Pronoe/millihom-meter/pcb_Kicad/pcb.jpg

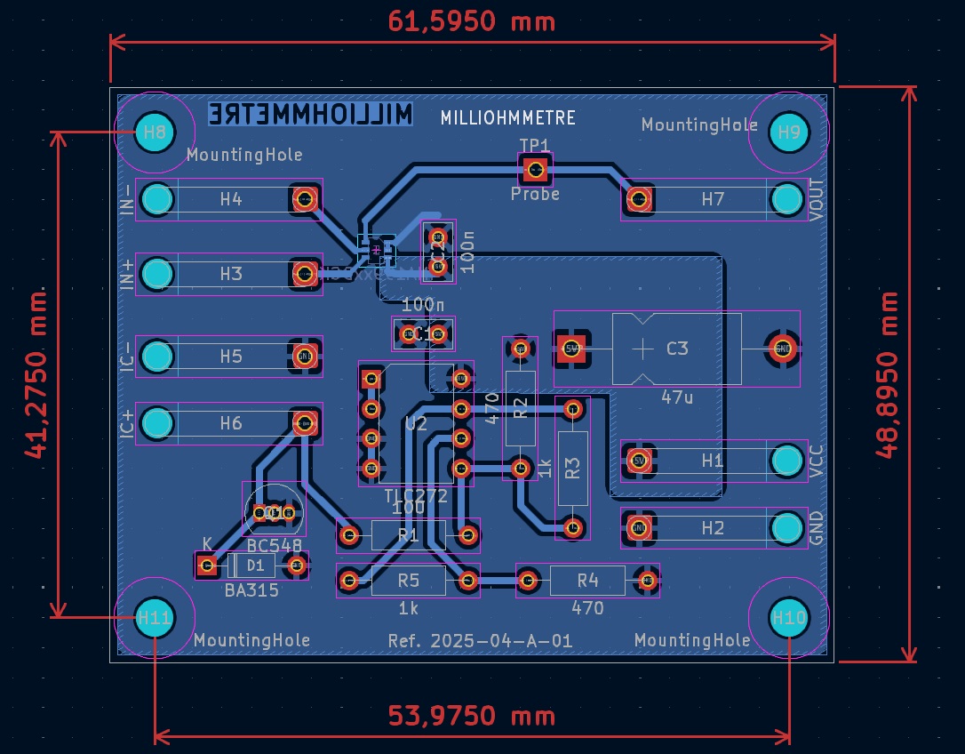
pcb_Kicad/pcb.jpg
