Pronoe/millihom-meter/pictures/20250501_192320 (FILEminimizer).jpg

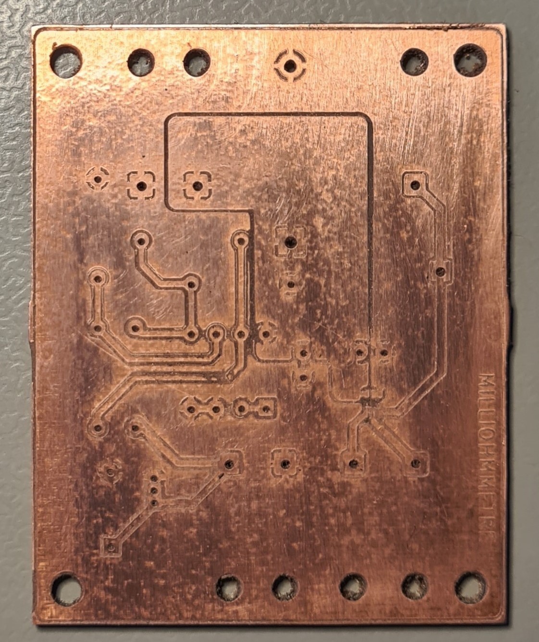
pictures/20250501_192320 (FILEminimizer).jpg
