Pronoe/millihom-meter/pictures/20250503_223159 (FILEminimizer).jpg

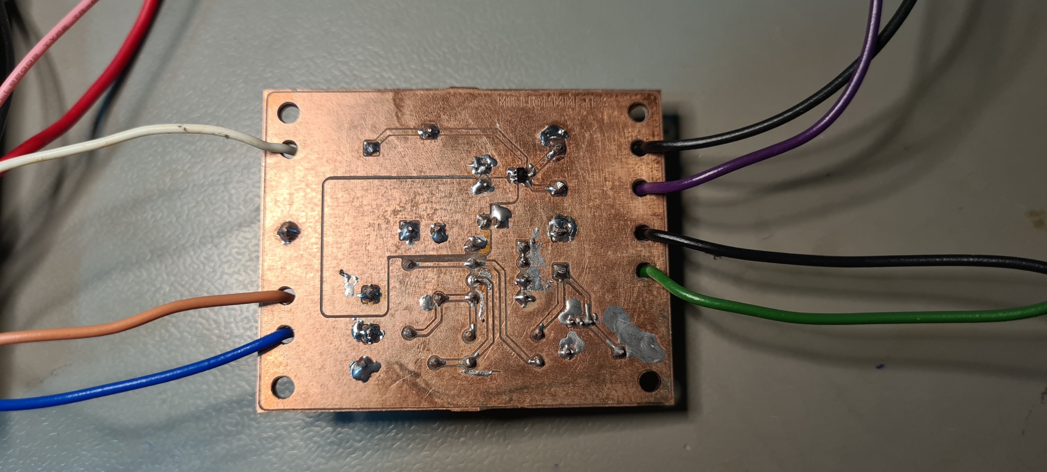
pictures/20250503_223159 (FILEminimizer).jpg
