Pronoe/millihom-meter/pictures/20250512_212327 (FILEminimizer).jpg

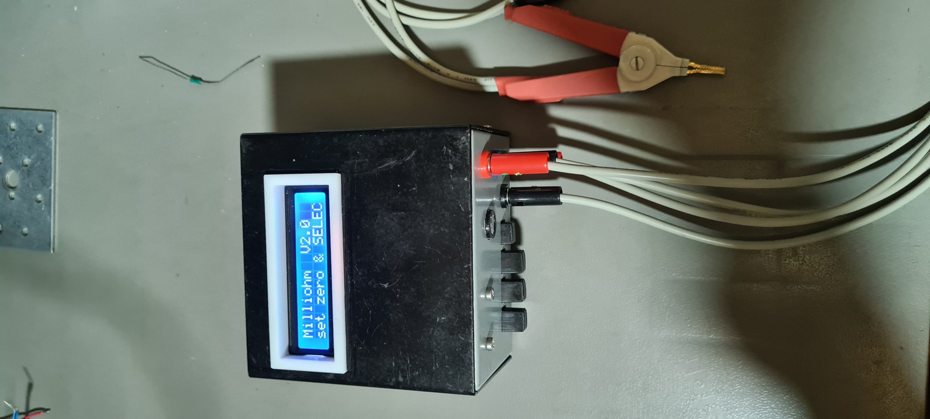
pictures/20250512_212327 (FILEminimizer).jpg
