Pronoe/millihom-meter/pictures/20250512_212805 (FILEminimizer).jpg

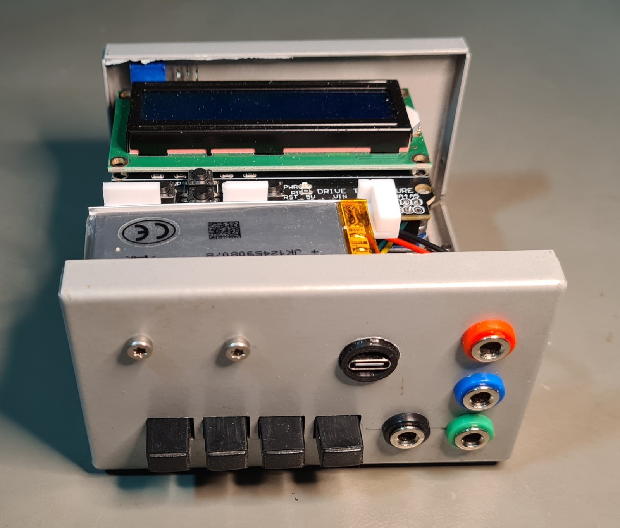
pictures/20250512_212805 (FILEminimizer).jpg
