Pronoe/millihom-meter/pictures/20250512_212813 (FILEminimizer).jpg

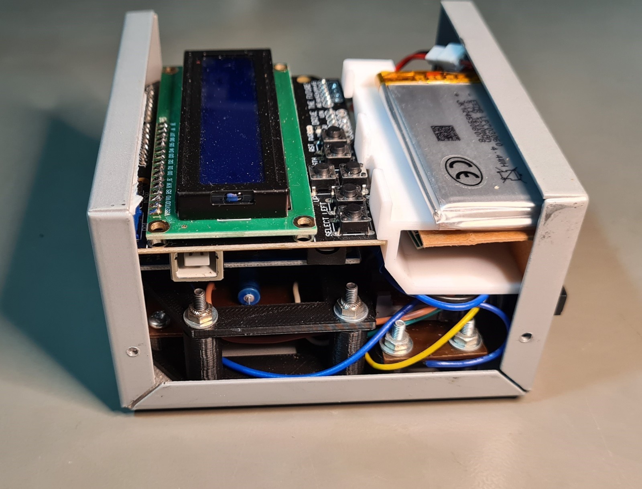
pictures/20250512_212813 (FILEminimizer).jpg
