Pronoe/millihom-meter/pictures/20250512_212826 (FILEminimizer).jpg

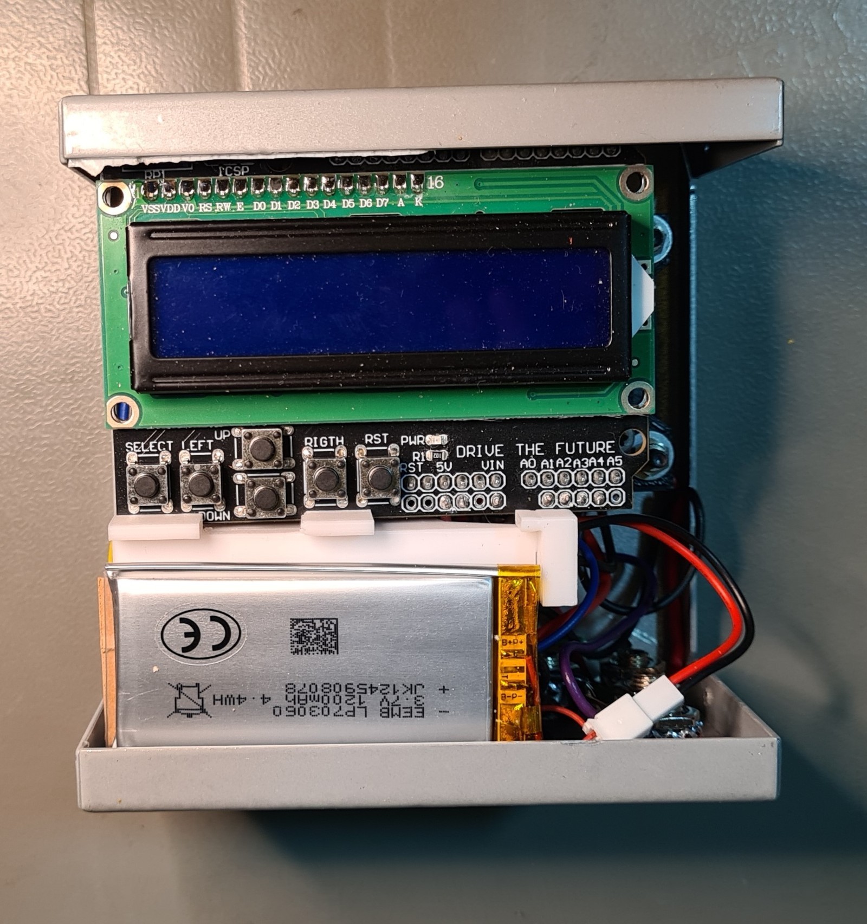
pictures/20250512_212826 (FILEminimizer).jpg
