Pronoe/millihom-meter/pictures/20250522_191747 (FILEminimizer).jpg

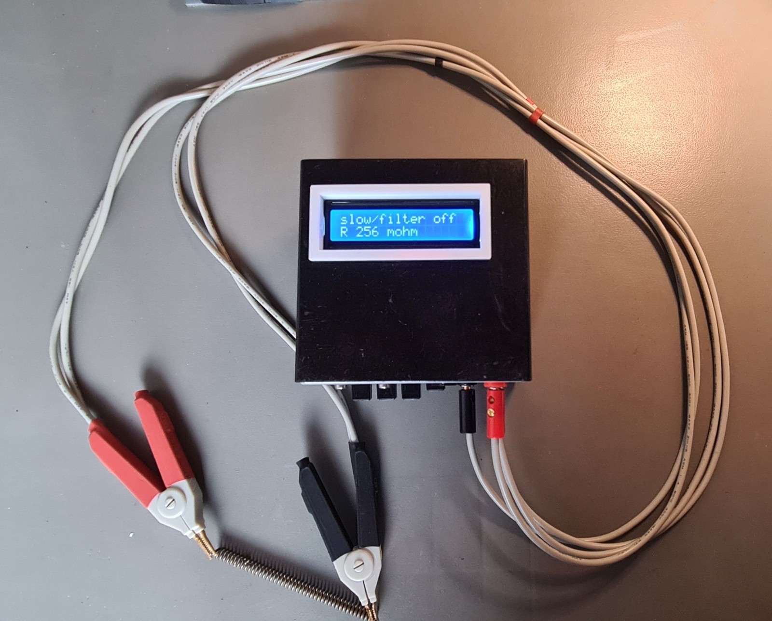
pictures/20250522_191747 (FILEminimizer).jpg
