Pronoe/millihom-meter/SW Arduino/Diagramme_SW_V1.png

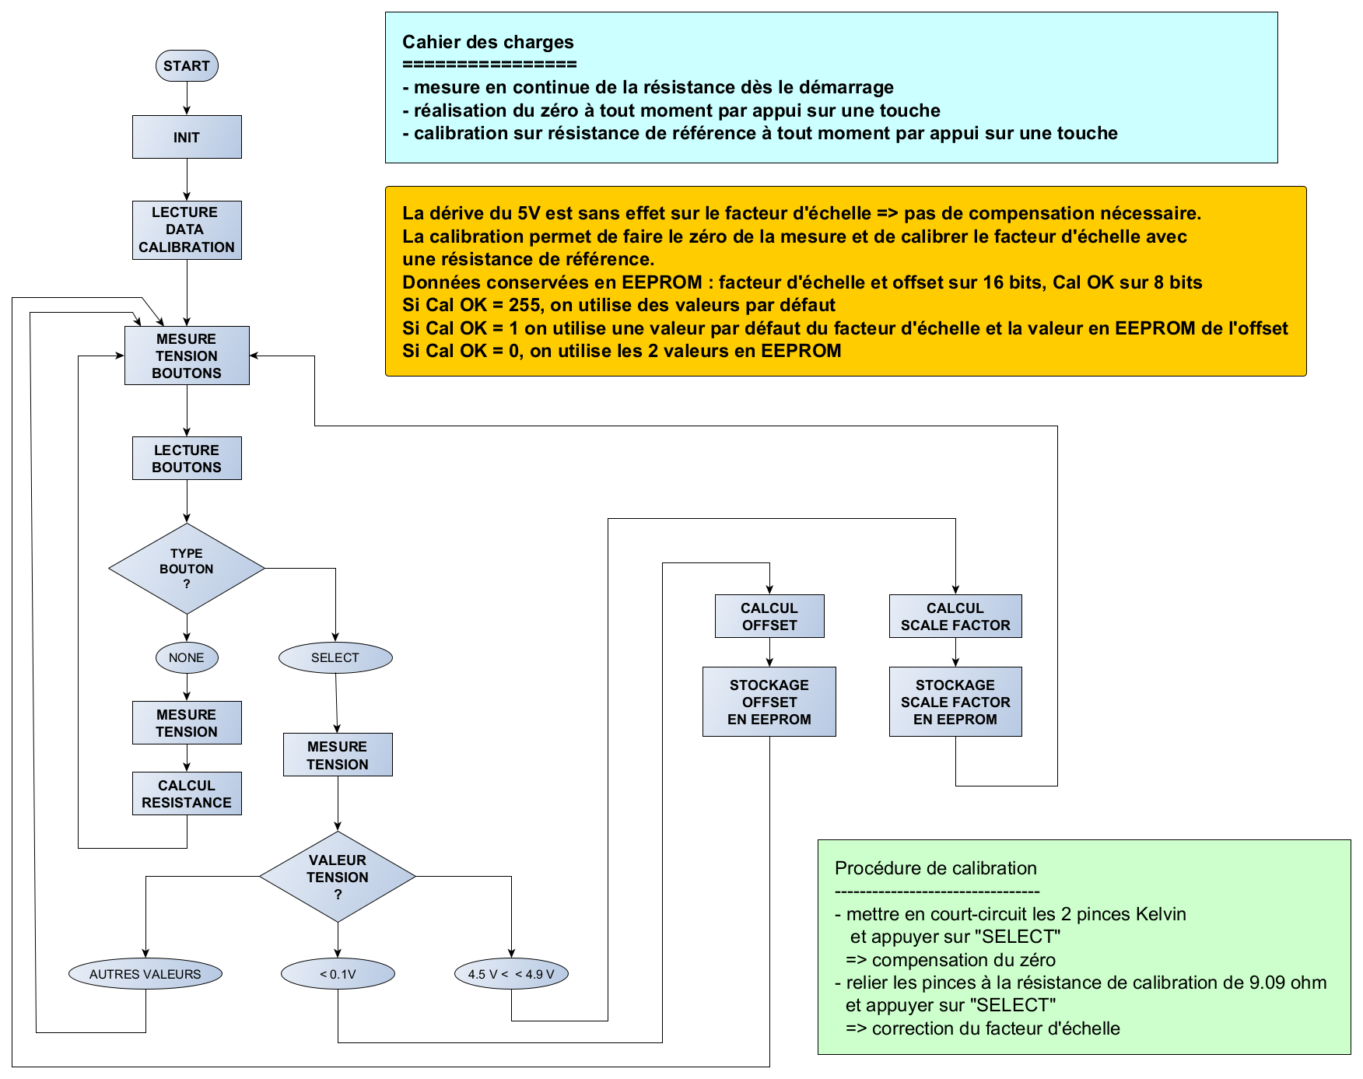
SW Arduino/Diagramme_SW_V1.png
